Brandovasq/Smart_Enviromental_Alarm_Clock/hardware/kicad/Light_Alarm.kicad_sch

## KiCad design hardware/kicad/Light_Alarm.kicad_sch (2026-05-27)

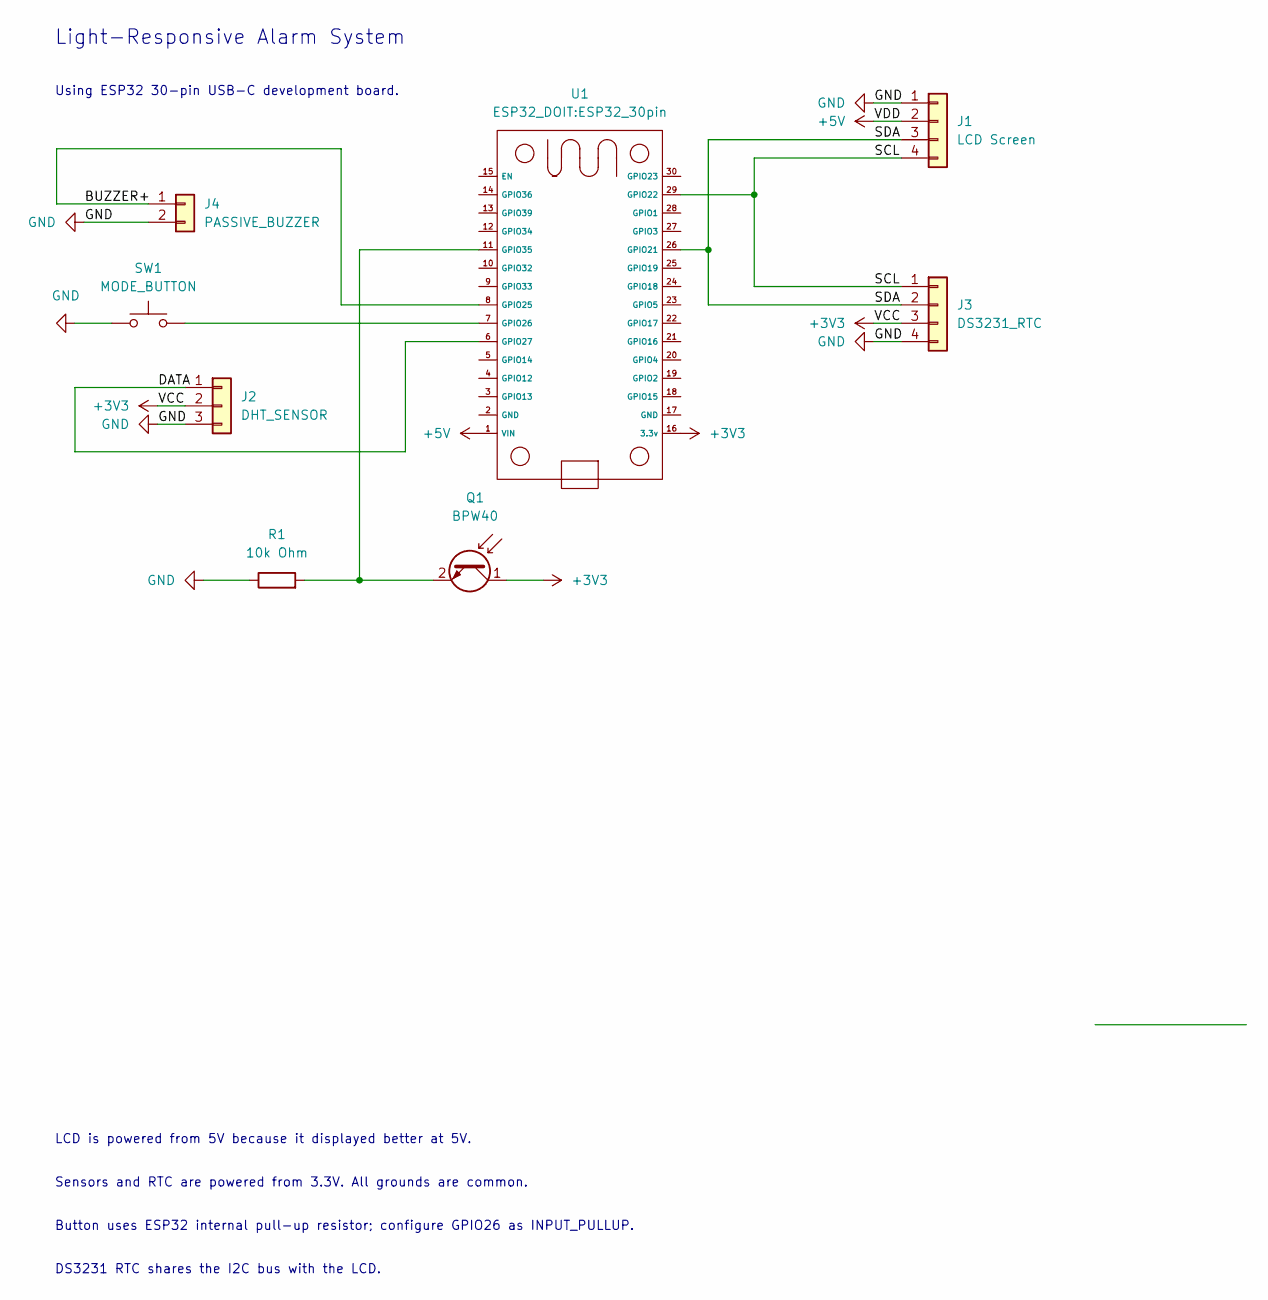
[picture p15: schematic Light_Alarm.kicad_sch]

Parts:
J1: LCD Screen
J2: DHT_SENSOR
J3: DS3231_RTC
J4: PASSIVE_BUZZER
Q1: BPW40; LED_D5.0mm_Clear
R1: 10k Ohm
SW1: MODE_BUTTON
U1: ESP32_30pin

Connections:
+3V3: J2.2, J3.3, Q1.1 (C), U1.16 (3.3v)
+5V: J1.2, U1.1 (VIN)
BUZZER+: J4.1, U1.8 (GPIO25)
DATA: J2.1, U1.6 (GPIO27)
GND: J1.1, J2.3, J3.4, J4.2, R1.1, SW1.1
unnamed: Q1.2 (E), R1.2, U1.11 (GPIO35)
unnamed: SW1.2, U1.7 (GPIO26)
SCL: J1.4, J3.1, U1.29 (GPIO22)
SDA: J1.3, J3.2, U1.26 (GPIO21)

Notes on the sheet:
DS3231 RTC shares the I2C bus with the LCD.
LCD is powered from 5V because it displayed better at 5V.
Using ESP32 30-pin USB-C development board.
Light-Responsive Alarm System
Button uses ESP32 internal pull-up resistor; configure GPIO26 as INPUT_PULLUP.
Sensors and RTC are powered from 3.3V. All grounds are common.
