Brandovasq/Smart_Enviromental_Alarm_Clock/src/light_responsive_alarm/config_example.h

#ifndef CONFIG_EXAMPLE_H
#define CONFIG_EXAMPLE_H

// Copy this file to config.h in the same folder as the sketch.
// Fill in your own Wi-Fi values locally and do not commit config.h.

const char* WIFI_SSID = "YOUR_WIFI_NAME";
const char* WIFI_PASSWORD = "YOUR_WIFI_PASSWORD";

#endif  // CONFIG_EXAMPLE_H
